Joseph-Wave/DS2HDMIconsolizer/XilinxProject DS-HDMI/DSHDMI.srcs/sources_1/imports/demo/test_card_squares.v

`timescale 1ns / 1ps
`default_nettype none

// Project F: Display Controller Test Card: Squares
// (C)2019 Will Green, Open Source Hardware released under the MIT License
// Learn more at https://projectf.io


// USE: Test Card: Squares - ENABLE ONE TEST CARD INSTANCE ONLY

//	test_card_squares #(
//		.H_RES(`H_RES),
//		.V_RES(`V_RES)
//	)
//	test_card_inst (
//		.i_x(sx),
//		.i_y(sy),
//		.o_red(red),
//		.o_green(green),
//		.o_blue(blue)
//	);


module test_card_squares #(
    H_RES=800,
    V_RES=600
    ) (
    input wire signed [15:0] i_x,
    input wire signed [15:0] i_y,
    output wire [7:0] o_red,
    output wire [7:0] o_green,
    output wire [7:0] o_blue
    );

    localparam HR = H_RES;              // horizontal resolution (pixels)
    localparam VR = V_RES;              // vertical resolution (lines)
    localparam BW = 16;                 // border width
    localparam SQ = VR >> 4;            // square unit
    localparam SX = (HR >> 1) - 5*SQ;   // square start horizontal
    localparam SY = (VR >> 1) - 5*SQ;   // square start vertical
    localparam LS = 2;                  // line spacing

    // Borders
    wire top = (i_x >=     0) & (i_y >=     0) & (i_x < HR) & (i_y < BW);
    wire btm = (i_x >=     0) & (i_y >= VR-BW) & (i_x < HR) & (i_y < VR);
    wire lft = (i_x >=     0) & (i_y >=     0) & (i_x < BW) & (i_y < VR);
    wire rgt = (i_x >= HR-BW) & (i_y >=     0) & (i_x < HR) & (i_y < VR);

    // Squares
    wire sq_a = (i_x >= SX)        & (i_y >= SY       ) & (i_x < SX +  4*SQ) & (i_y < SY +  4*SQ);
    wire sq_b = (i_x >= SX + 2*SQ) & (i_y >= SY + 2*SQ) & (i_x < SX +  6*SQ) & (i_y < SY +  6*SQ);
    wire sq_c = (i_x >= SX + 4*SQ) & (i_y >= SY + 4*SQ) & (i_x < SX +  8*SQ) & (i_y < SY +  8*SQ);
    wire sq_d = (i_x >= SX + 6*SQ) & (i_y >= SY + 6*SQ) & (i_x < SX + 10*SQ) & (i_y < SY + 10*SQ);
    wire sq_e = (i_x >= SX)        & (i_y >= SY + 8*SQ) & (i_x < SX +  2*SQ) & (i_y < SY + 10*SQ);

    // Lines
    wire lns_1 = (i_x >= SX + 8*SQ) & (i_x <= SX + 10*SQ) & ((i_y == SY + 0*LS       ) | (i_y == SY +  2*SQ - 0*LS));
    wire lns_2 = (i_x >= SX + 8*SQ) & (i_x <= SX + 10*SQ) & ((i_y == SY + 1*LS       ) | (i_y == SY +  2*SQ - 1*LS));
    wire lns_3 = (i_x >= SX + 8*SQ) & (i_x <= SX + 10*SQ) & ((i_y == SY + 2*LS       ) | (i_y == SY +  2*SQ - 2*LS));
    wire lns_4 = (i_x >= SX + 8*SQ) & (i_x <= SX + 10*SQ) & ((i_y == SY + 3*LS       ) | (i_y == SY +  2*SQ - 3*LS));
    wire lns_5 = (i_y >=        SY) & (i_y <= SY +  2*SQ) & ((i_x == SX + 8*SQ + 0*LS) | (i_x == SX + 10*SQ - 0*LS));
    wire lns_6 = (i_y >=        SY) & (i_y <= SY +  2*SQ) & ((i_x == SX + 8*SQ + 1*LS) | (i_x == SX + 10*SQ - 1*LS));
    wire lns_7 = (i_y >=        SY) & (i_y <= SY +  2*SQ) & ((i_x == SX + 8*SQ + 2*LS) | (i_x == SX + 10*SQ - 2*LS));
    wire lns_8 = (i_y >=        SY) & (i_y <= SY +  2*SQ) & ((i_x == SX + 8*SQ + 3*LS) | (i_x == SX + 10*SQ - 3*LS));

    // Colour Output
    assign o_red    = {8{ lft | top | lns_1 | lns_4 | lns_5 | lns_8 | sq_b | sq_e }};
    assign o_green  = {8{ btm | top | lns_2 | lns_4 | lns_6 | lns_8 | sq_a | sq_d | sq_e }};
    assign o_blue   = {8{ rgt | top | lns_3 | lns_4 | lns_7 | lns_8 | sq_c | sq_e }};
endmodule
